StHack/badge-2026/hardware/images/face/eye-left.png

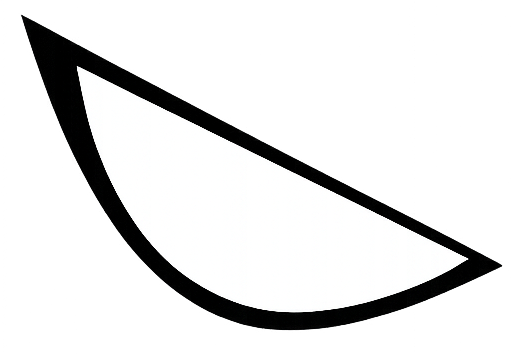
hardware/images/face/eye-left.png
