StHack/badge-2026/hardware/images/face/eye-right.png

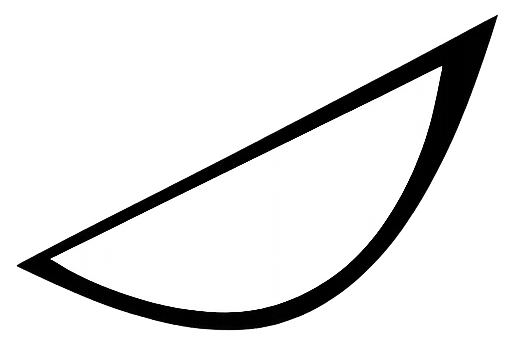
hardware/images/face/eye-right.png
