StHack/badge-2026/hardware/images/shield/inverted-stripes.png

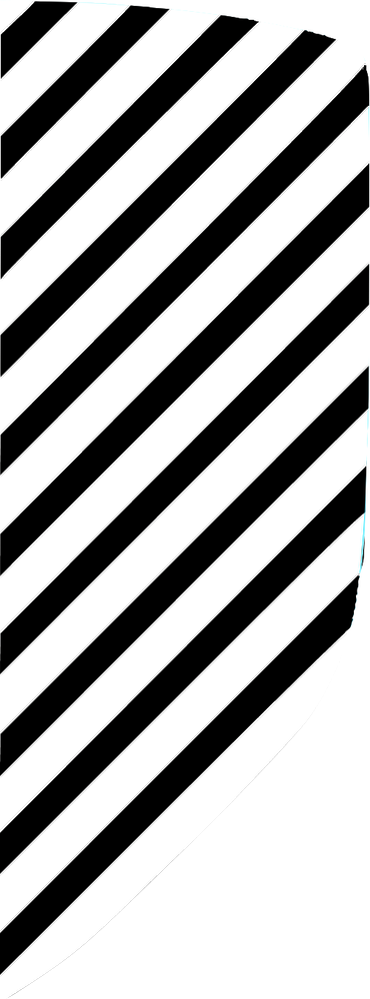
hardware/images/shield/inverted-stripes.png
