StHack/badge-2026/hardware/images/shield/shield-full.png

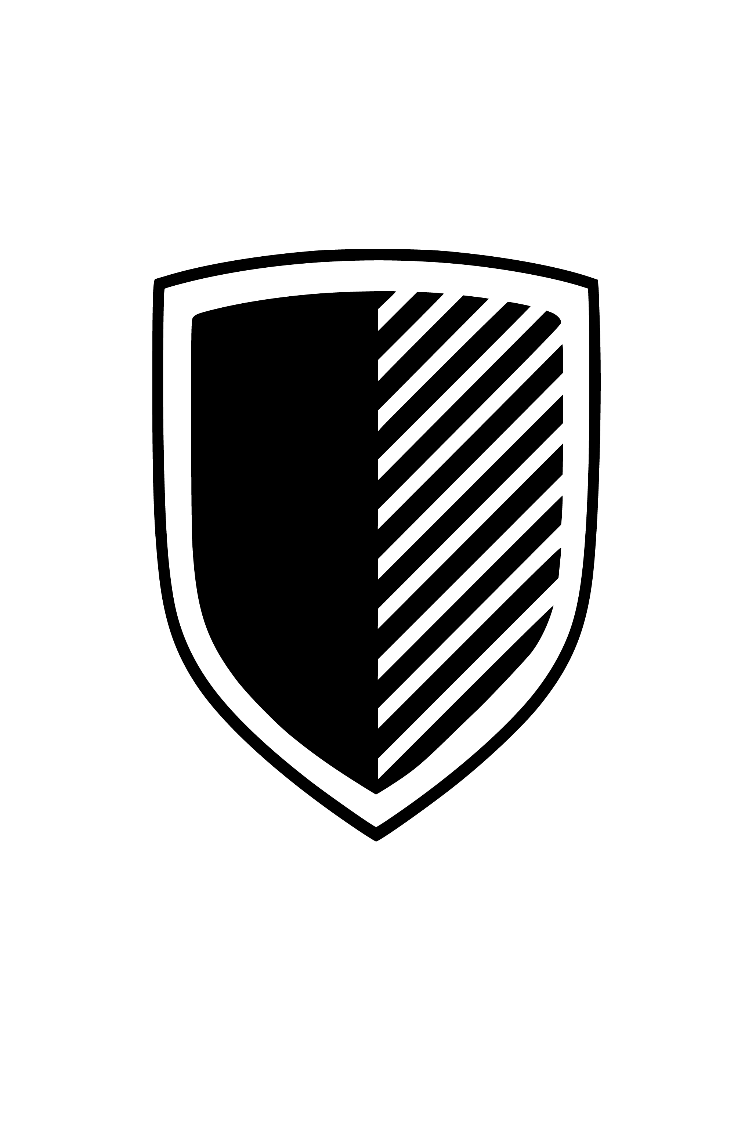
hardware/images/shield/shield-full.png
