StHack/badge-2026/hardware/images/shield/shield-stripes.png

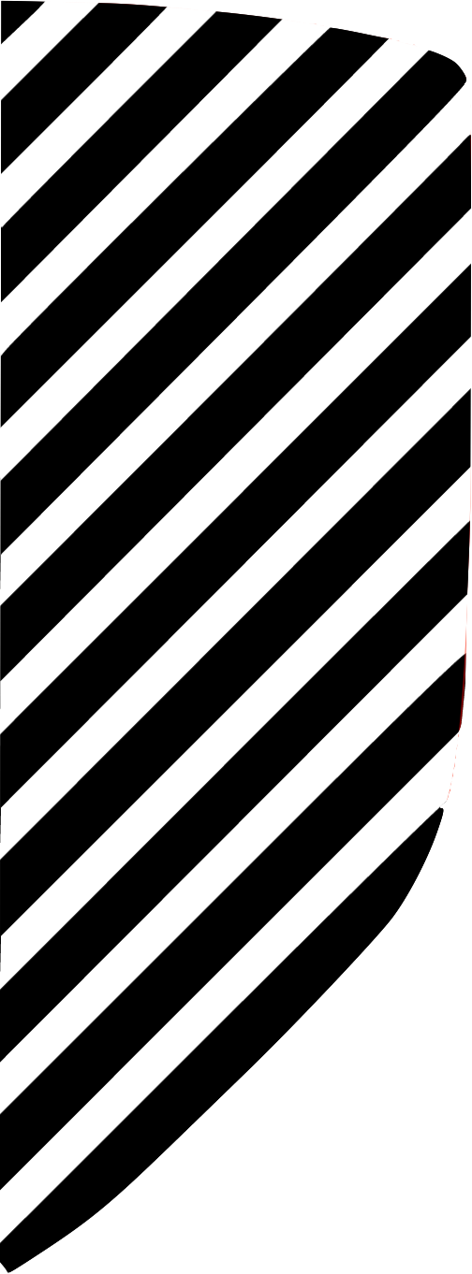
hardware/images/shield/shield-stripes.png
