StHack/badge-2026/hardware/images/shield/shield.png

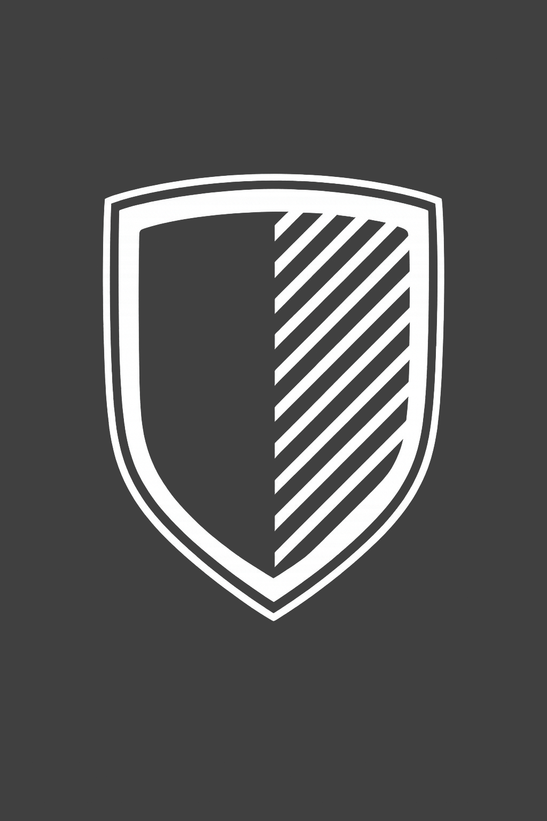
hardware/images/shield/shield.png
