StHack/badge-2026/images/back.jpg

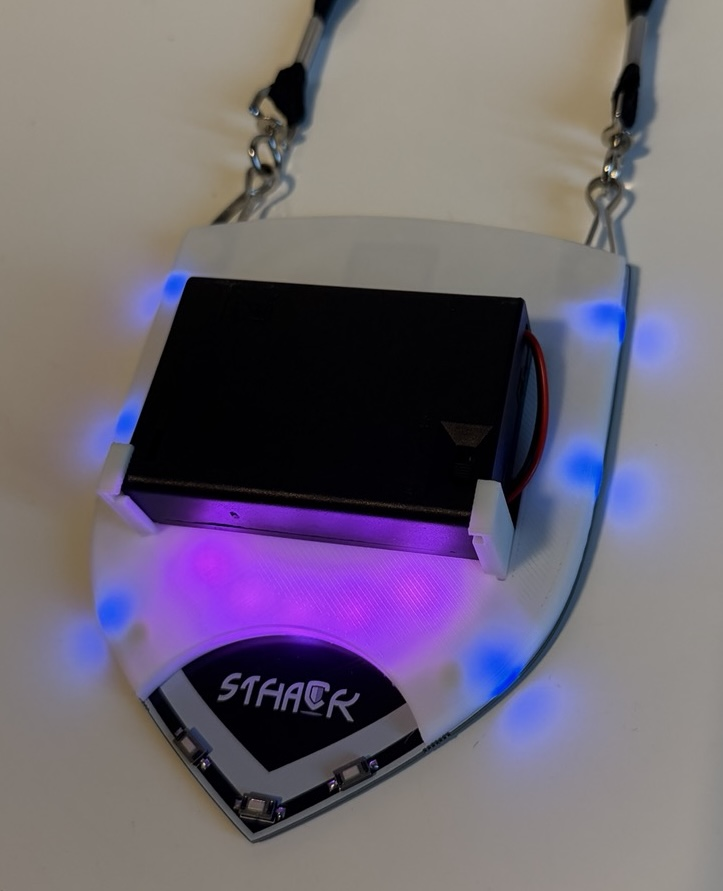
images/back.jpg
