StHack/badge-2026/images/image.jpg

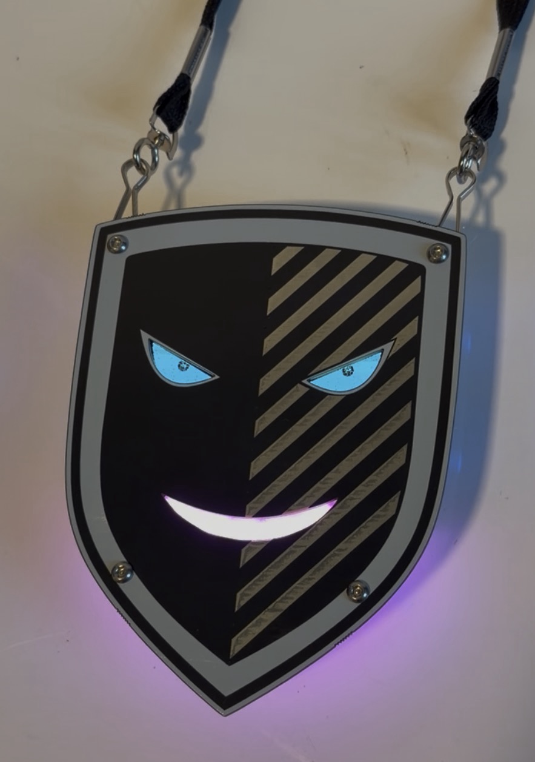
images/image.jpg
