StHack/badge-2026/hardware/components-datasheets/SSD1306-shape.jpeg

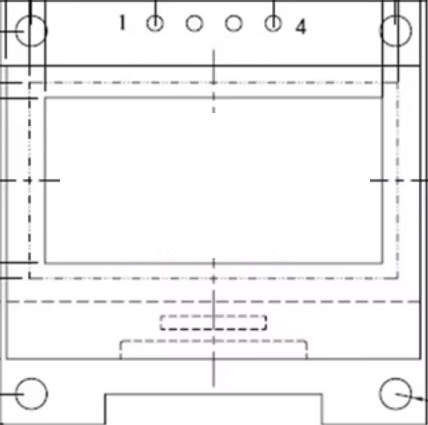
hardware/components-datasheets/SSD1306-shape.jpeg
