StHack/badge-2026/hardware/components-datasheets/SSD1306.jpeg

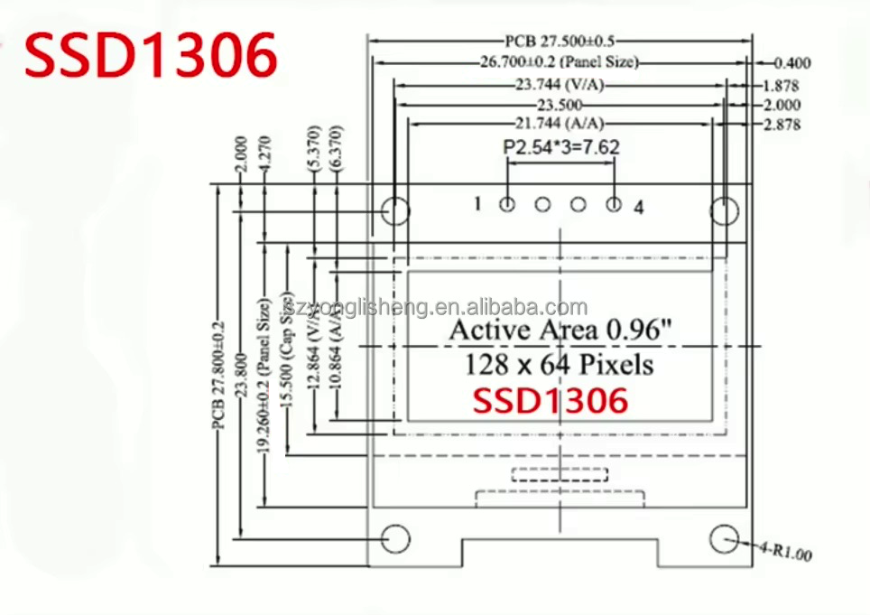
hardware/components-datasheets/SSD1306.jpeg
